rafaelmartins/pico-synth/firmware/tui/driver-oled-font.c

/********************************************************************************
 * Copyright (c) 2012, Majenko Technologies
 * Copyright (c) 2016, zaltora
 * Copyright (c) 2019, Rafael G. Martins <rafael@rafaelmartins.eng.br>
 * All rights reserved.
 *
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
 * THIS SOFTWARE IS PROVIDED BY THE COPYRIGHT HOLDERS AND CONTRIBUTORS "AS IS" AND
 * ANY EXPRESS OR IMPLIED WARRANTIES, INCLUDING, BUT NOT LIMITED TO, THE IMPLIED
 * WARRANTIES OF MERCHANTABILITY AND FITNESS FOR A PARTICULAR PURPOSE ARE
 * DISCLAIMED. IN NO EVENT SHALL THE COPYRIGHT OWNER OR CONTRIBUTORS BE LIABLE FOR
 * ANY DIRECT, INDIRECT, INCIDENTAL, SPECIAL, EXEMPLARY, OR CONSEQUENTIAL DAMAGES
 * (INCLUDING, BUT NOT LIMITED TO, PROCUREMENT OF SUBSTITUTE GOODS OR SERVICES;
 * LOSS OF USE, DATA, OR PROFITS; OR BUSINESS INTERRUPTION) HOWEVER CAUSED AND
 * ON ANY THEORY OF LIABILITY, WHETHER IN CONTRACT, STRICT LIABILITY, OR TORT
 * (INCLUDING NEGLIGENCE OR OTHERWISE) ARISING IN ANY WAY OUT OF THE USE OF THIS
 * SOFTWARE, EVEN IF ADVISED OF THE POSSIBILITY OF SUCH DAMAGE.
 *
 * The views and conclusions contained in the software and documentation are those
 * of the authors and should not be interpreted as representing official policies,
 * either expressed or implied, of the FreeBSD Project.
 ********************************************************************************/

// this is glcd 5x7 font, modified from the version of it available at:
// https://github.com/SuperHouse/esp-open-rtos/blob/7432c01/extras/fonts/data/font_glcd_5x7.h

#include <stdint.h>

const uint8_t font_bitmaps[] =
{
    /* @0 '\x0' (5 pixels wide) */
    0x00, //
    0x00, //
    0x00, //
    0x00, //
    0x00, //
    0x00, //
    0x00, //

    /* @7 '\x1' (5 pixels wide) */
    0x70, //  ###
    0xF8, // #####
    0xA8, // # # #
    0xF8, // #####
    0xD8, // ## ##
    0x88, // #   #
    0x70, //  ###

    /* @14 '\x2' (5 pixels wide) */
    0x70, //  ###
    0xF8, // #####
    0xA8, // # # #
    0xF8, // #####
    0x88, // #   #
    0xD8, // ## ##
    0x70, //  ###

    /* @21 '\x3' (5 pixels wide) */
    0x00, //
    0x50, //  # #
    0xF8, // #####
    0xF8, // #####
    0xF8, // #####
    0x70, //  ###
    0x20, //   #

    /* @28 '\x4' (5 pixels wide) */
    0x00, //
    0x20, //   #
    0x70, //  ###
    0xF8, // #####
    0xF8, // #####
    0x70, //  ###
    0x20, //   #

    /* @35 '\x5' (5 pixels wide) */
    0x70, //  ###
    0x50, //  # #
    0xF8, // #####
    0xA8, // # # #
    0xF8, // #####
    0x20, //   #
    0x70, //  ###

    /* @42 '\x6' (5 pixels wide) */
    0x20, //   #
    0x70, //  ###
    0xF8, // #####
    0xF8, // #####
    0xF8, // #####
    0x20, //   #
    0x70, //  ###

    /* @49 '\x7' (5 pixels wide) */
    0x00, //
    0x00, //
    0x20, //   #
    0x70, //  ###
    0x70, //  ###
    0x20, //   #
    0x00, //

    /* @56 '\x8' (5 pixels wide) */
    0xF8, // #####
    0xF8, // #####
    0xD8, // ## ##
    0x88, // #   #
    0x88, // #   #
    0xD8, // ## ##
    0xF8, // #####

    /* @63 '\x9' (5 pixels wide) */
    0x00, //
    0x00, //
    0x20, //   #
    0x50, //  # #
    0x50, //  # #
    0x20, //   #
    0x00, //

    /* @70 '\xA' (5 pixels wide) */
    0xF8, // #####
    0xF8, // #####
    0xD8, // ## ##
    0xA8, // # # #
    0xA8, // # # #
    0xD8, // ## ##
    0xF8, // #####

    /* @77 '\xB' (5 pixels wide) */
    0x00, //
    0x38, //   ###
    0x18, //    ##
    0x68, //  ## #
    0xA0, // # #
    0xA0, // # #
    0x40, //  #

    /* @84 '\xC' (5 pixels wide) */
    0x70, //  ###
    0x88, // #   #
    0x88, // #   #
    0x70, //  ###
    0x20, //   #
    0xF8, // #####
    0x20, //   #

    /* @91 '\xD' (5 pixels wide) */
    0x78, //  ####
    0x48, //  #  #
    0x78, //  ####
    0x40, //  #
    0x40, //  #
    0x40, //  #
    0xC0, // ##

    /* @98 '\xE' (5 pixels wide) */
    0x78, //  ####
    0x48, //  #  #
    0x78, //  ####
    0x48, //  #  #
    0x48, //  #  #
    0x58, //  # ##
    0xC0, // ##

    /* @105 '\xF' (5 pixels wide) */
    0x20, //   #
    0xA8, // # # #
    0x70, //  ###
    0xD8, // ## ##
    0xD8, // ## ##
    0x70, //  ###
    0xA8, // # # #

    /* @112 '\x10' (5 pixels wide) */
    0x80, // #
    0xC0, // ##
    0xF0, // ####
    0xF8, // #####
    0xF0, // ####
    0xC0, // ##
    0x80, // #

    /* @119 '\x11' (5 pixels wide) */
    0x08, //     #
    0x18, //    ##
    0x78, //  ####
    0xF8, // #####
    0x78, //  ####
    0x18, //    ##
    0x08, //     #

    /* @126 '\x12' (5 pixels wide) */
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
    0x00, //
    0xE8, // ### #
    0xB8, // # ###
    0x00, //
    0xE8, // ### #
    0xB8, // # ###
    0x00, //

    /* @1729 '\xF7' (5 pixels wide) */
    0x70, //  ###
    0xD8, // ## ##
    0xD8, // ## ##
    0x70, //  ###
    0x00, //
    0x00, //
    0x00, //

    /* @1736 '\xF8' (5 pixels wide) */
    0x00, //
    0x00, //
    0x00, //
    0x30, //   ##
    0x30, //   ##
    0x00, //
    0x00, //

    /* @1743 '\xF9' (5 pixels wide) */
    0x00, //
    0x00, //
    0x00, //
    0x00, //
    0x30, //   ##
    0x00, //
    0x00, //

    /* @1750 '\xFA' (5 pixels wide) */
    0x38, //   ###
    0x20, //   #
    0x20, //   #
    0x20, //   #
    0xA0, // # #
    0xA0, // # #
    0x60, //  ##

    /* @1757 '\xFB' (5 pixels wide) */
    0x70, //  ###
    0x48, //  #  #
    0x48, //  #  #
    0x48, //  #  #
    0x48, //  #  #
    0x00, //
    0x00, //

    /* @1764 '\xFC' (5 pixels wide) */
    0x70, //  ###
    0x18, //    ##
    0x30, //   ##
    0x60, //  ##
    0x78, //  ####
    0x00, //
    0x00, //

    /* @1771 '\xFD' (5 pixels wide) */
    0x00, //
    0x00, //
    0x78, //  ####
    0x78, //  ####
    0x78, //  ####
    0x78, //  ####
    0x00, //

    /* @1778 '\xFE' (5 pixels wide) */
    0x00, //
    0x00, //
    0x00, //
    0x00, //
    0x00, //
    0x00, //
    0x00, //

    /* @1785 '\xFF' (5 pixels wide) */
    0x08, //     #
    0x28, //   # #
    0x08, //     #
    0x28, //   # #
    0x00, //
    0x78, //  ####
    0x08, //     #

};

const uint16_t font_descriptors[] =
{
    0,     /* \x00 */
    7,     /* \x01 */
    14,    /* \x02 */
    21,    /* \x03 */
    28,    /* \x04 */
    35,    /* \x05 */
    42,    /* \x06 */
    49,    /* \x07 */
    56,    /* \x08 */
    63,    /* \x09 */
    70,    /* \x0A */
    77,    /* \x0B */
    84,    /* \x0C */
    91,    /* \x0D */
    98,    /* \x0E */
    105,   /* \x0F */
    112,   /* \x10 */
    119,   /* \x11 */
    126,   /* \x12 */
    133,   /* \x13 */
    140,   /* \x14 */
    147,   /* \x15 */
    154,   /* \x16 */
    161,   /* \x17 */
    168,   /* \x18 */
    175,   /* \x19 */
    182,   /* \x1A */
    189,   /* \x1B */
    196,   /* \x1C */
    203,   /* \x1D */
    210,   /* \x1E */
    217,   /* \x1F */
    224,   /*      */
    231,   /*   !  */
    238,   /*   "  */
    245,   /*   #  */
    252,   /*   $  */
    259,   /*   %  */
    266,   /*   &  */
    273,   /*   '  */
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
    1120,  /* \xA0 */
    1127,  /* \xA1 */
    1134,  /* \xA2 */
    1141,  /* \xA3 */
    1148,  /* \xA4 */
    1155,  /* \xA5 */
    1162,  /* \xA6 */
    1169,  /* \xA7 */
    1176,  /* \xA8 */
    1183,  /* \xA9 */
    1190,  /* \xAA */
    1197,  /* \xAB */
    1204,  /* \xAC */
    1211,  /* \xAD */
    1218,  /* \xAE */
    1225,  /* \xAF */
    1232,  /* \xB0 */
    1239,  /* \xB1 */
    1246,  /* \xB2 */
    1253,  /* \xB3 */
    1260,  /* \xB4 */
    1267,  /* \xB5 */
    1274,  /* \xB6 */
    1281,  /* \xB7 */
    1288,  /* \xB8 */
    1295,  /* \xB9 */
    1302,  /* \xBA */
    1309,  /* \xBB */
    1316,  /* \xBC */
    1323,  /* \xBD */
    1330,  /* \xBE */
    1337,  /* \xBF */
    1344,  /* \xC0 */
    1351,  /* \xC1 */
    1358,  /* \xC2 */
    1365,  /* \xC3 */
    1372,  /* \xC4 */
    1379,  /* \xC5 */
    1386,  /* \xC6 */
    1393,  /* \xC7 */
    1400,  /* \xC8 */
    1407,  /* \xC9 */
    1414,  /* \xCA */
    1421,  /* \xCB */
    1428,  /* \xCC */
    1435,  /* \xCD */
    1442,  /* \xCE */
    1449,  /* \xCF */
    1456,  /* \xD0 */
    1463,  /* \xD1 */
    1470,  /* \xD2 */
    1477,  /* \xD3 */
    1484,  /* \xD4 */
    1491,  /* \xD5 */
    1498,  /* \xD6 */
    1505,  /* \xD7 */
    1512,  /* \xD8 */
    1519,  /* \xD9 */
    1526,  /* \xDA */
    1533,  /* \xDB */
    1540,  /* \xDC */
    1547,  /* \xDD */
    1554,  /* \xDE */
    1561,  /* \xDF */
    1568,  /* \xE0 */
    1575,  /* \xE1 */
    1582,  /* \xE2 */
    1589,  /* \xE3 */
    1596,  /* \xE4 */
    1603,  /* \xE5 */
    1610,  /* \xE6 */
    1617,  /* \xE7 */
    1624,  /* \xE8 */
    1631,  /* \xE9 */
    1638,  /* \xEA */
    1645,  /* \xEB */
    1652,  /* \xEC */
    1659,  /* \xED */
    1666,  /* \xEE */
    1673,  /* \xEF */
    1680,  /* \xF0 */
    1687,  /* \xF1 */
    1694,  /* \xF2 */
    1701,  /* \xF3 */
    1708,  /* \xF4 */
    1715,  /* \xF5 */
    1722,  /* \xF6 */
    1729,  /* \xF7 */
    1736,  /* \xF8 */
    1743,  /* \xF9 */
    1750,  /* \xFA */
    1757,  /* \xFB */
    1764,  /* \xFC */
    1771,  /* \xFD */
    1778,  /* \xFE */
    1785,  /* \xFF */
};
