rafaelmartins/pico-synth/firmware/midi/include/tusb_config.h

/*
 * The MIT License (MIT)
 *
 * Copyright (c) 2019 Ha Thach (tinyusb.org)
 * Copyright (c) 2021 Rafael G. Martins <rafael@rafaelmartins.eng.br>
 *
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
 */

#ifndef _TUSB_CONFIG_H_
#define _TUSB_CONFIG_H_

#ifdef __cplusplus
 extern "C" {
#endif

//--------------------------------------------------------------------
// COMMON CONFIGURATION
//--------------------------------------------------------------------

// defined by compiler flags for flexibility
#ifndef CFG_TUSB_MCU
  #error CFG_TUSB_MCU must be defined
#endif

#define CFG_TUSB_RHPORT0_MODE     OPT_MODE_DEVICE

#ifndef CFG_TUSB_OS
#define CFG_TUSB_OS                 OPT_OS_PICO
#endif

#ifndef CFG_TUSB_MEM_SECTION
#define CFG_TUSB_MEM_SECTION
#endif

#ifndef CFG_TUSB_MEM_ALIGN
#define CFG_TUSB_MEM_ALIGN          __attribute__ ((aligned(4)))
#endif

//--------------------------------------------------------------------
// DEVICE CONFIGURATION
//--------------------------------------------------------------------

#ifndef CFG_TUD_ENDPOINT0_SIZE
#define CFG_TUD_ENDPOINT0_SIZE    64
#endif

//------------- CLASS -------------//
#define CFG_TUD_HID             0
#define CFG_TUD_CDC             0
#define CFG_TUD_MSC             0
#define CFG_TUD_MIDI            1
#define CFG_TUD_VENDOR          0

#define CFG_TUD_MIDI_RX_BUFSIZE (TUD_OPT_HIGH_SPEED ? 512 : 64)
#define CFG_TUD_MIDI_TX_BUFSIZE (TUD_OPT_HIGH_SPEED ? 512 : 64)

#ifdef __cplusplus
 }
#endif

#endif /* _TUSB_CONFIG_H_ */
